S34m1n4t0r/health_sense/pcb/calc/SimUVopamp.asc

C1: cap; 100n
I1: current; 200n
R1: res; 7Meg
R2: res; 3,3k
R3: res; 400
R4: res; 100Meg
U2: AD8091
V1: voltage; 3
Named nets: 0, 5V0, out
.tran 4 startup
